filipas123/autonomous-computer/4x-6000/photos/4gpu/introduction/rack3.jpg

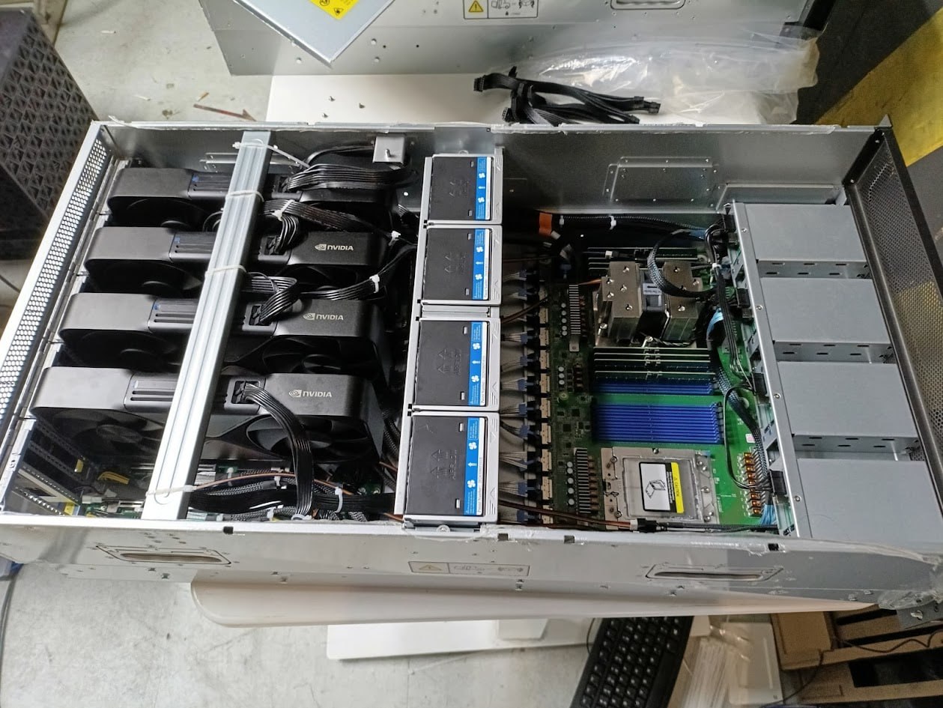
4x-6000/photos/4gpu/introduction/rack3.jpg
