filipas123/autonomous-computer/4x-6000/photos/4gpu/preparing/ee/card1.jpg

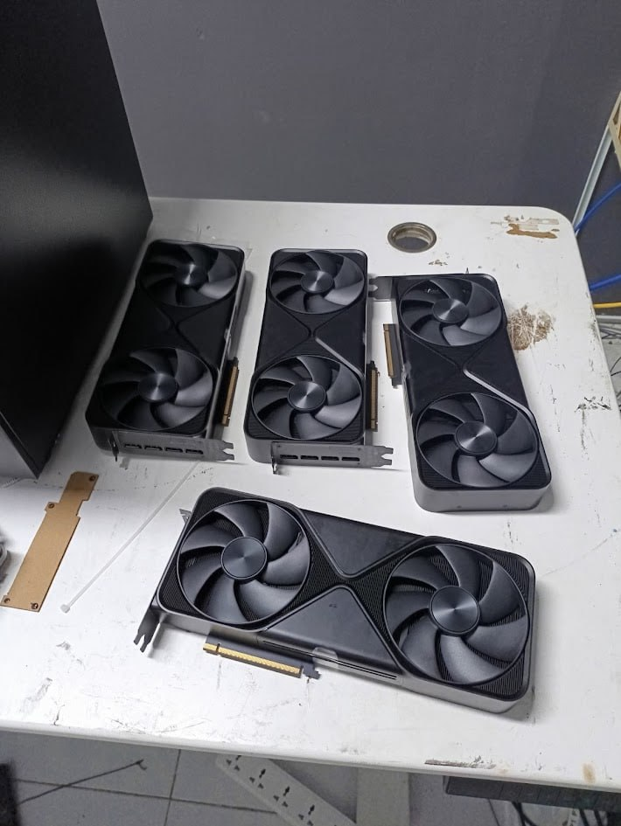
4x-6000/photos/4gpu/preparing/ee/card1.jpg
