filipas123/autonomous-computer/8x-5090/photos/8gpu/introduction/EdgeAI-8GPU-2.png

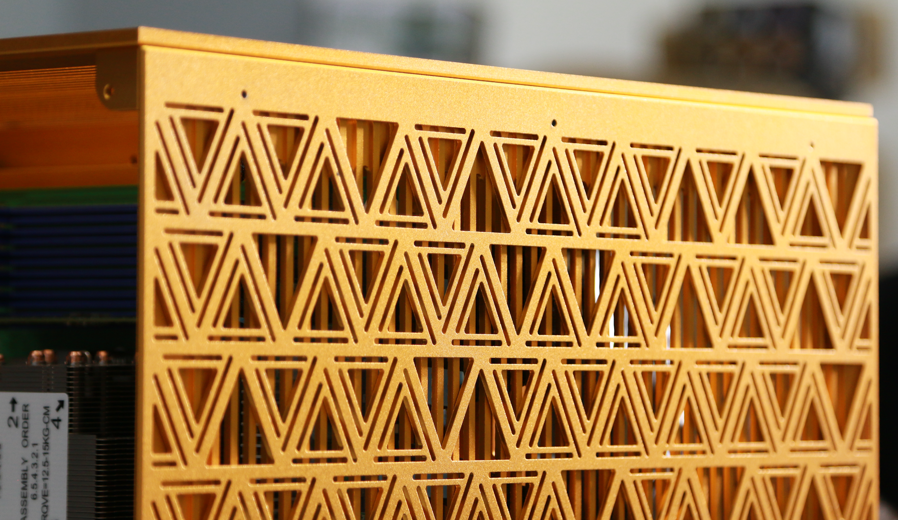
8x-5090/photos/8gpu/introduction/EdgeAI-8GPU-2.png
