filipas123/autonomous-computer/8x-5090/photos/8gpu/preparing/ee/inside-8card.jpg

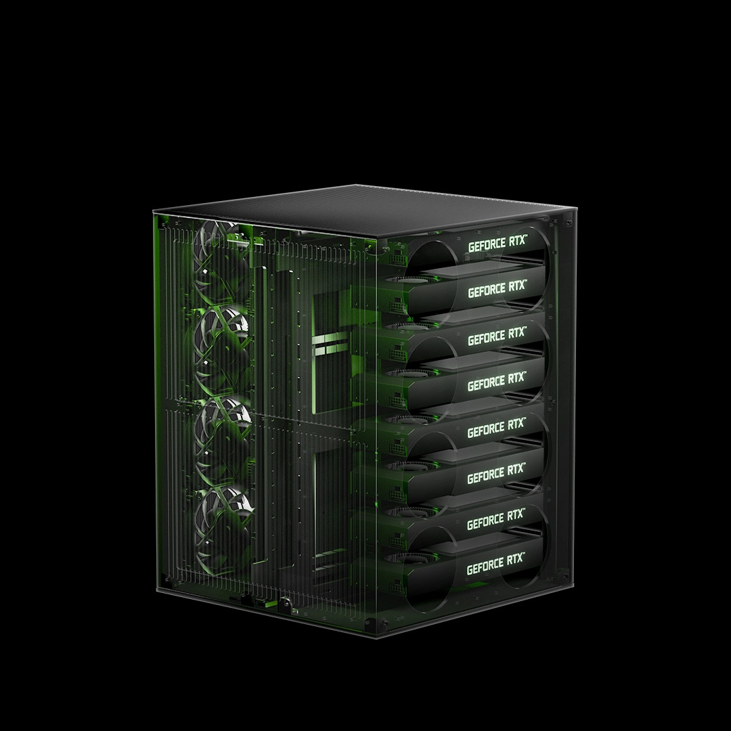
8x-5090/photos/8gpu/preparing/ee/inside-8card.jpg
