filipas123/autonomous-computer/4x-5090/step_models/Part 1 - Bottom.step

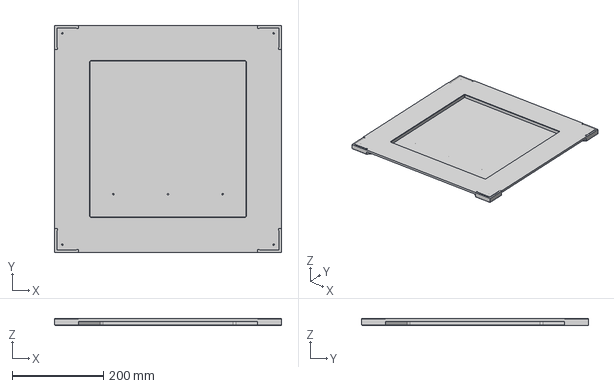
[picture p86: CAD file, 2026-07-07]
4x-5090/step_models/Part 1 - Bottom.step
498.0 x 498.0 x 15.0 mm
