filipas123/autonomous-computer/8x-5090/step_models/GPU mount.step

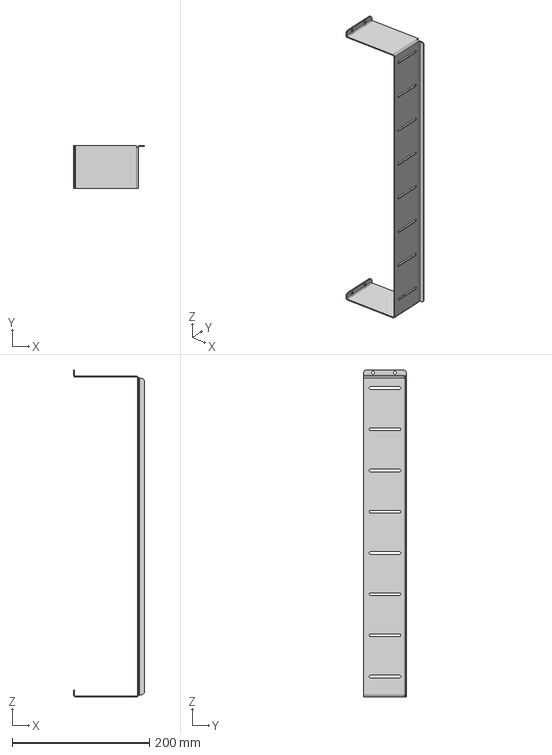
[picture p87: CAD file, 2025-08-18]
8x-5090/step_models/GPU mount.step
103.5 x 63.0 x 476.0 mm
