filipas123/autonomous-computer/2x-5090/step_models/Part 5 - Middle.step

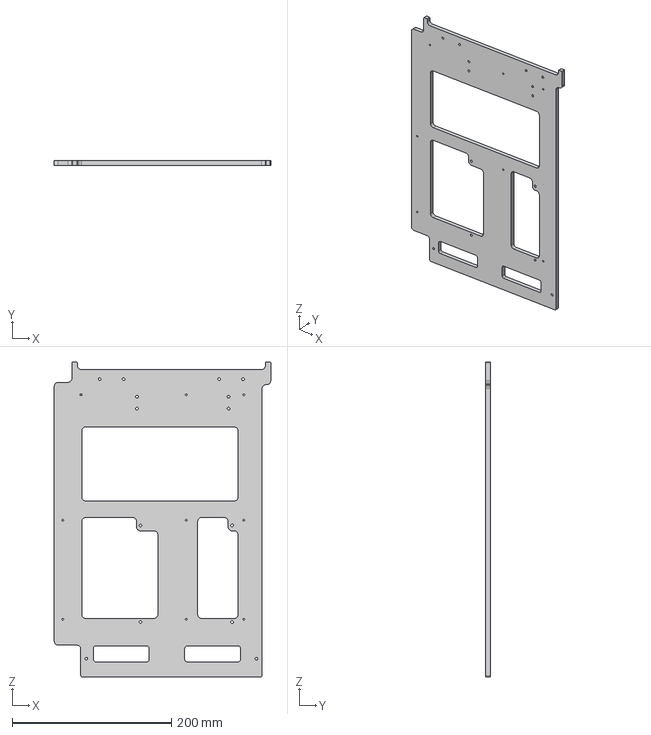
[picture p88: CAD file, 2026-06-01]
2x-5090/step_models/Part 5 - Middle.step
271.9 x 6.00 x 395.5 mm
