filipas123/autonomous-computer/4x-5090/step_models/9 Fan mount.step

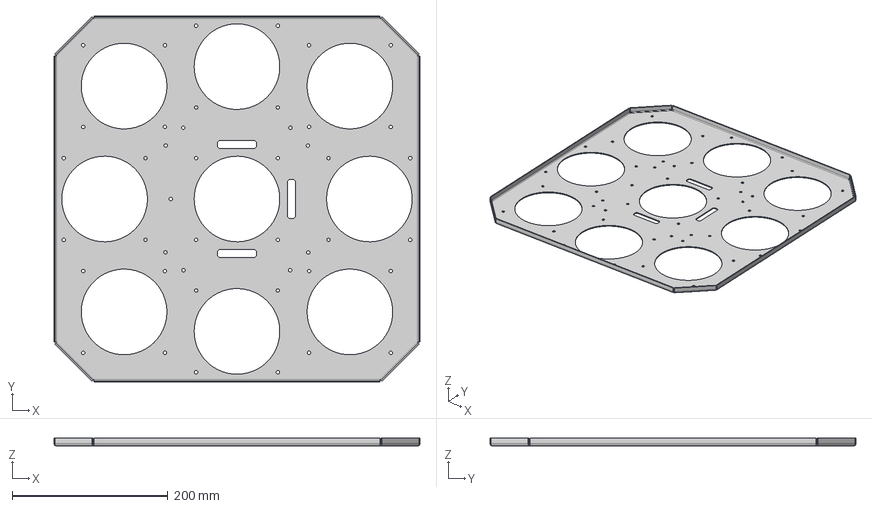
[picture p89: CAD file, 2026-07-07]
4x-5090/step_models/9 Fan mount.step
470.0 x 470.0 x 10.0 mm
