filipas123/autonomous-computer/8x-5090/step_models/Part 5 - Bottom.step

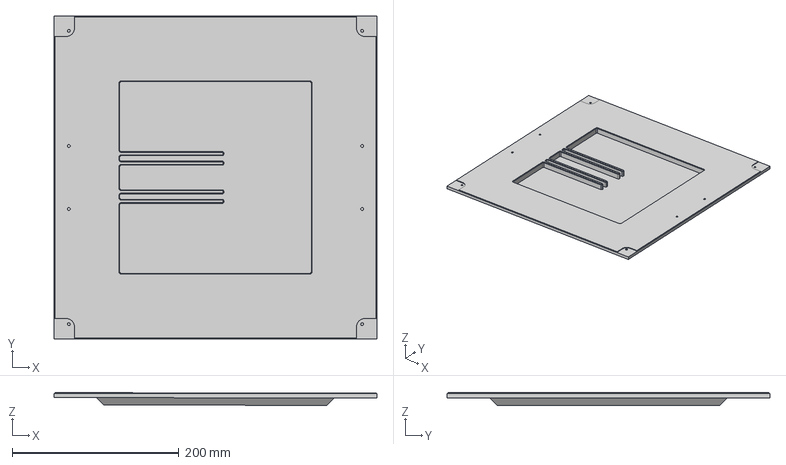
[picture p90: CAD file, 2025-08-18]
8x-5090/step_models/Part 5 - Bottom.step
387.6 x 387.6 x 15.0 mm
