filipas123/autonomous-computer/2x-5090/step_models/Part 4 - Bottom.step

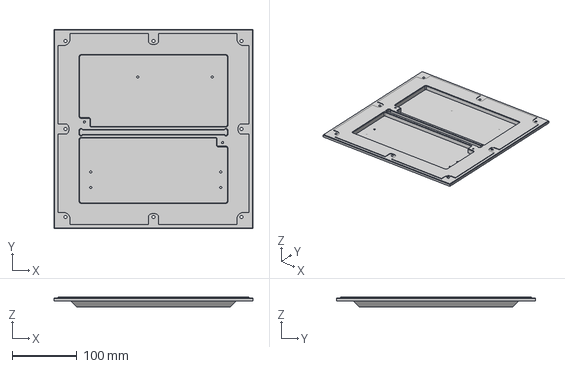
[picture p91: CAD file, 2026-06-01]
2x-5090/step_models/Part 4 - Bottom.step
307.6 x 307.6 x 15.0 mm
