filipas123/autonomous-computer/4x-5090/step_models/GPU mount.step

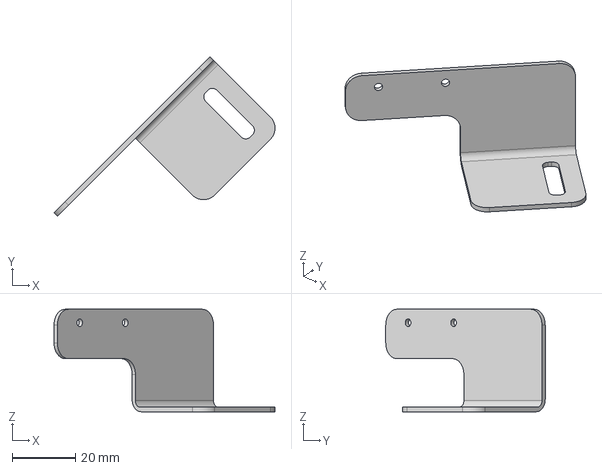
[picture p92: CAD file, 2026-07-07]
4x-5090/step_models/GPU mount.step
70.0 x 50.6 x 32.5 mm
