filipas123/autonomous-computer/8x-5090/step_models/Support.step

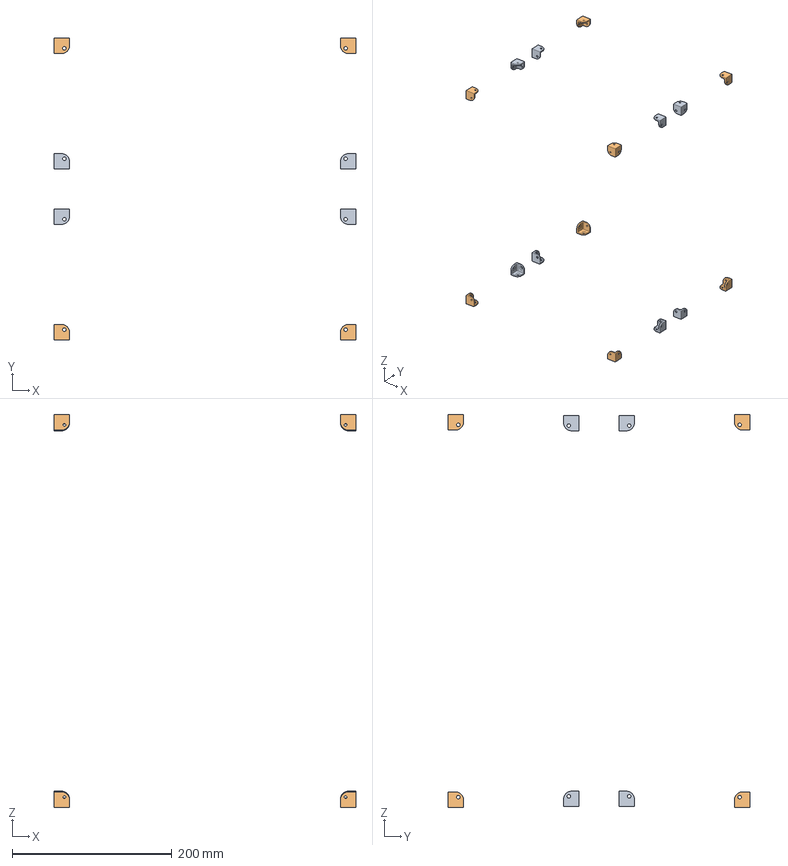
[picture p93: CAD file, 2025-08-18]
8x-5090/step_models/Support.step
378.0 x 378.0 x 492.0 mm
Bat goc x 8
Bat goc (1) x 4
Bat goc (1)(Mirror)
Bat goc (1) (2)(Mirror)
Bat goc (1) (3)(Mirror)
Bat goc (1) (1)(Mirror)
