filipas123/autonomous-computer/2x-5090/step_models/GPU mount 1.step

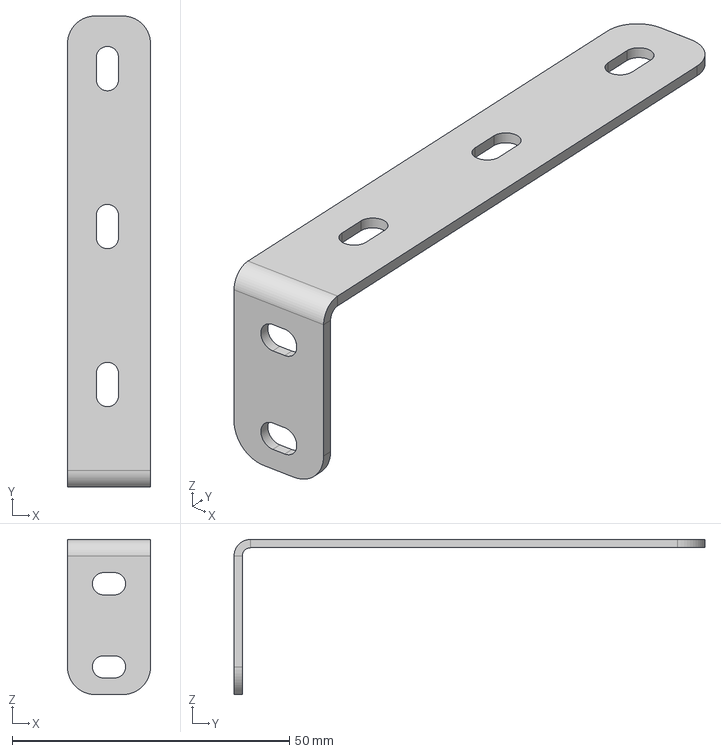
[picture p94: CAD file, 2026-06-01]
2x-5090/step_models/GPU mount 1.step
15.0 x 85.0 x 28.0 mm
