filipas123/autonomous-computer/4x-5090/step_models/Part 3 - Top.step

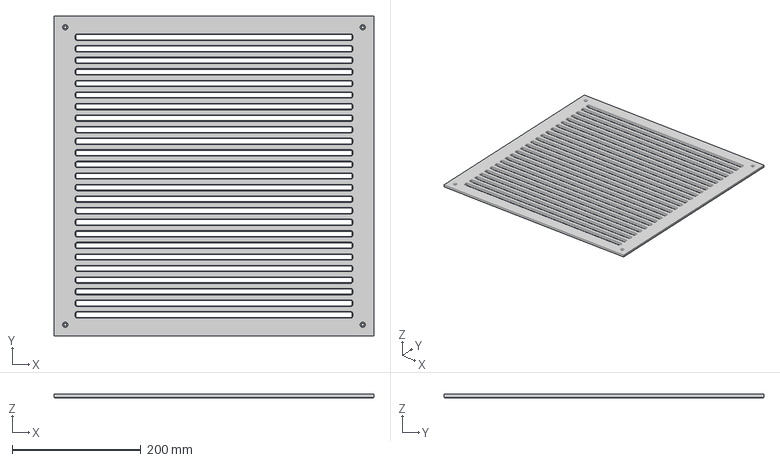
[picture p95: CAD file, 2026-07-07]
4x-5090/step_models/Part 3 - Top.step
498.0 x 498.0 x 6.00 mm
