filipas123/autonomous-computer/8x-5090/step_models/Part 1 - GPU plate.step

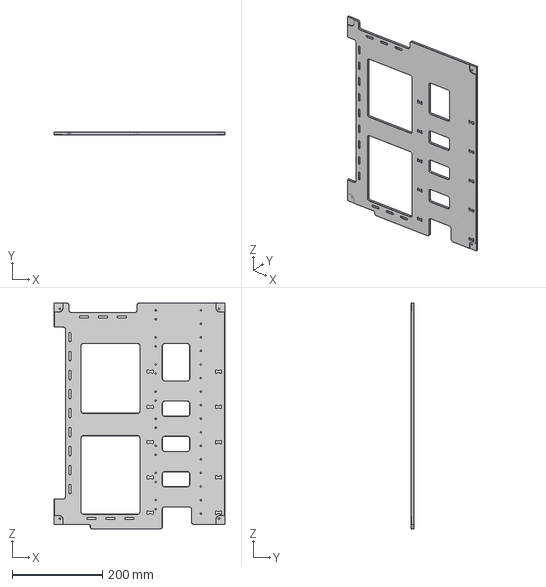
[picture p96: CAD file, 2025-08-18]
8x-5090/step_models/Part 1 - GPU plate.step
378.0 x 6.00 x 500.0 mm
