filipas123/autonomous-computer/4x-5090/step_models/Part 6 - Corner 2.step

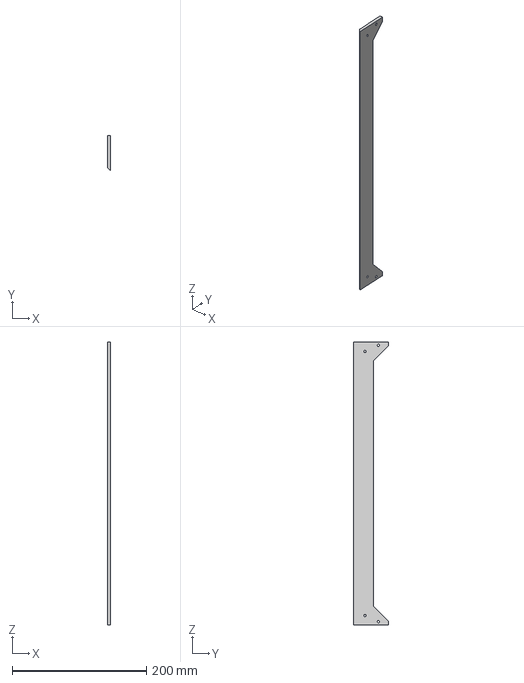
[picture p97: CAD file, 2026-07-07]
4x-5090/step_models/Part 6 - Corner 2.step
5.00 x 52.0 x 421.5 mm
