filipas123/autonomous-computer/8x-5090/step_models/Ethernet mount.step

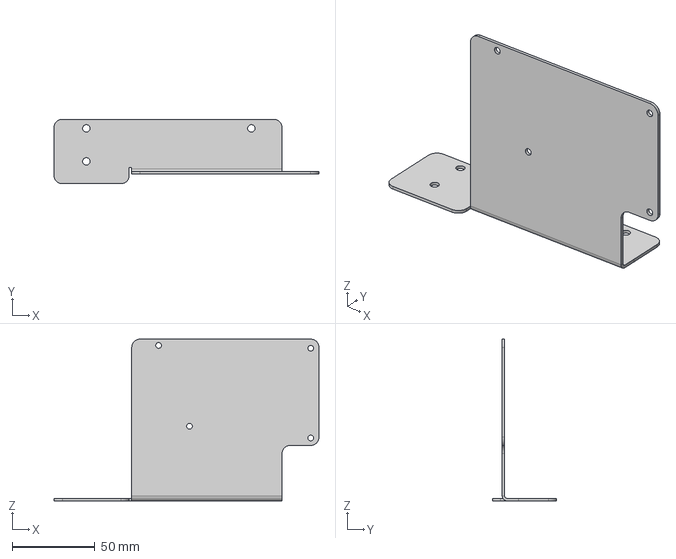
[picture p98: CAD file, 2025-08-18]
8x-5090/step_models/Ethernet mount.step
160.6 x 39.0 x 98.0 mm
