filipas123/autonomous-computer/4x-5090/step_models/Part 2 - Back.step

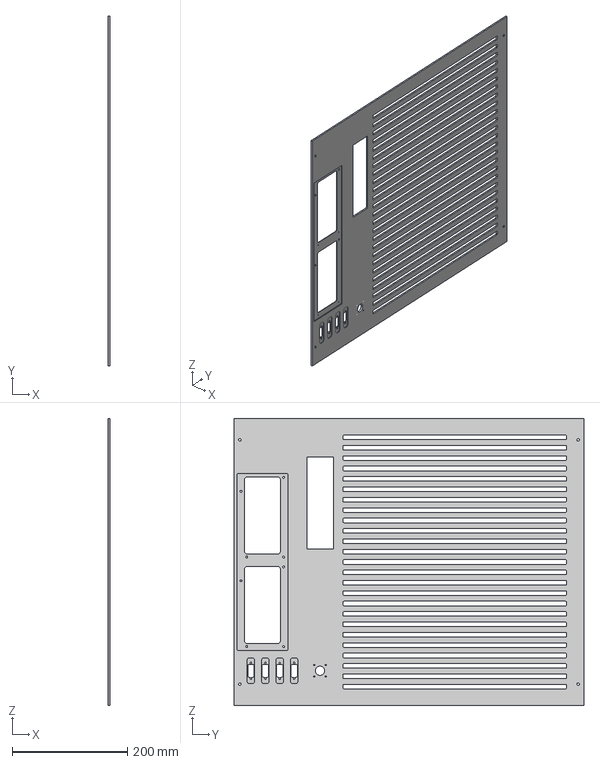
[picture p99: CAD file, 2026-07-07]
4x-5090/step_models/Part 2 - Back.step
4.00 x 606.5 x 498.0 mm
