filipas123/autonomous-computer/4x-5090/step_models/Corner mount.step

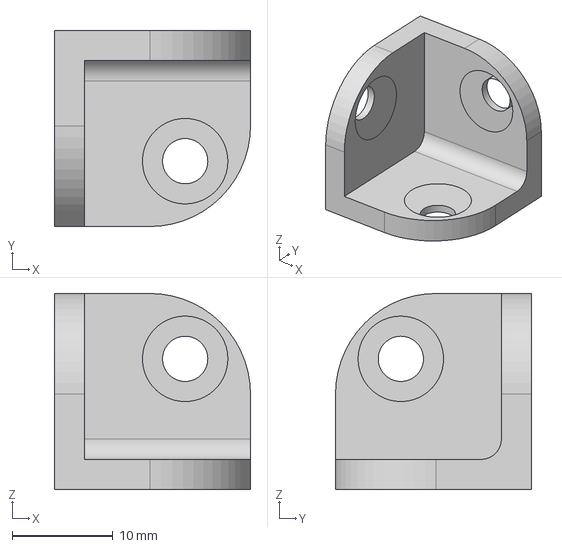
[picture p101: CAD file, 2026-07-07]
4x-5090/step_models/Corner mount.step
19.5 x 19.5 x 19.5 mm
