filipas123/autonomous-computer/4x-5090/step_models/Part 5 - Corner 1.step

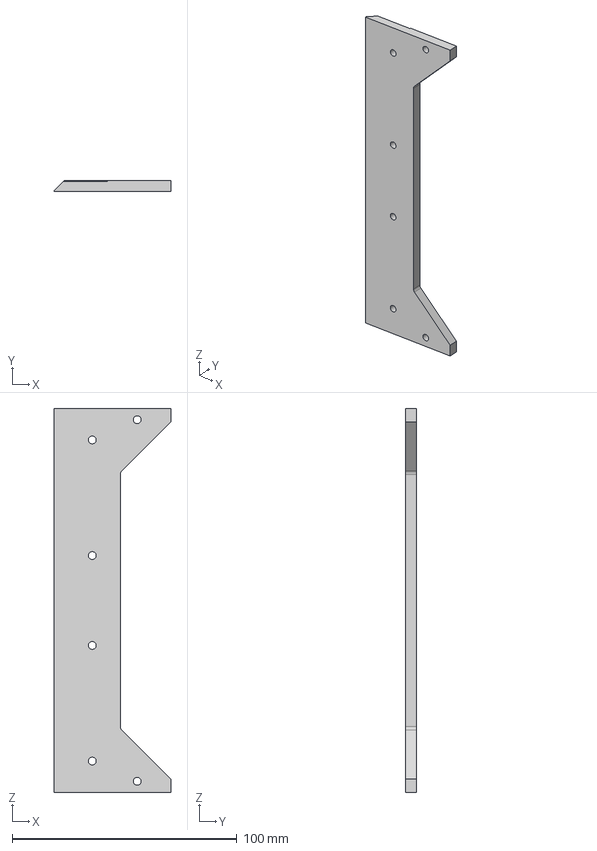
[picture p102: CAD file, 2026-07-07]
4x-5090/step_models/Part 5 - Corner 1.step
52.0 x 5.00 x 171.0 mm
