filipas123/autonomous-computer/4x-5090/step_models/Part 4 - Middle.step

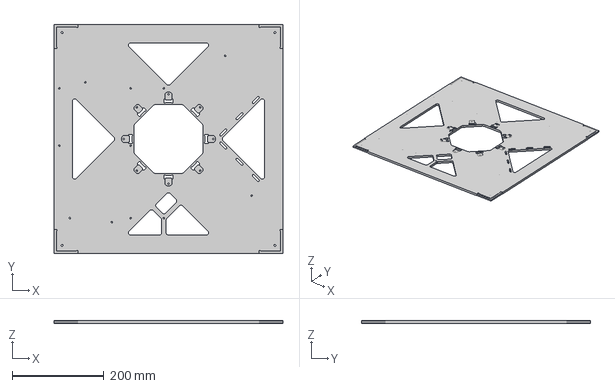
[picture p103: CAD file, 2026-07-07]
4x-5090/step_models/Part 4 - Middle.step
498.0 x 498.0 x 6.00 mm
