filipas123/autonomous-computer/4x-5090/step_models/Part 7 - GPU Holder 1.step

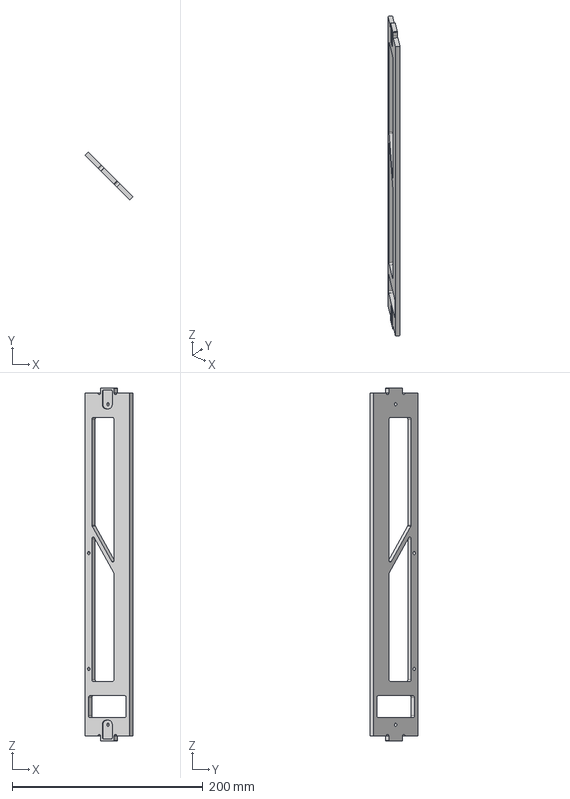
[picture p104: CAD file, 2026-07-07]
4x-5090/step_models/Part 7 - GPU Holder 1.step
50.2 x 50.2 x 370.0 mm
