filipas123/autonomous-computer/4x-5090/step_models/L mount.step

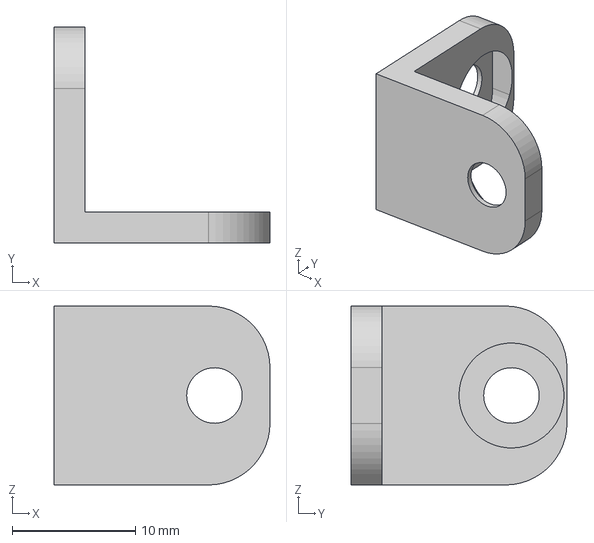
[picture p105: CAD file, 2026-07-07]
4x-5090/step_models/L mount.step
17.5 x 17.5 x 14.5 mm
