filipas123/autonomous-computer/4x-6000/build-4x.jpg

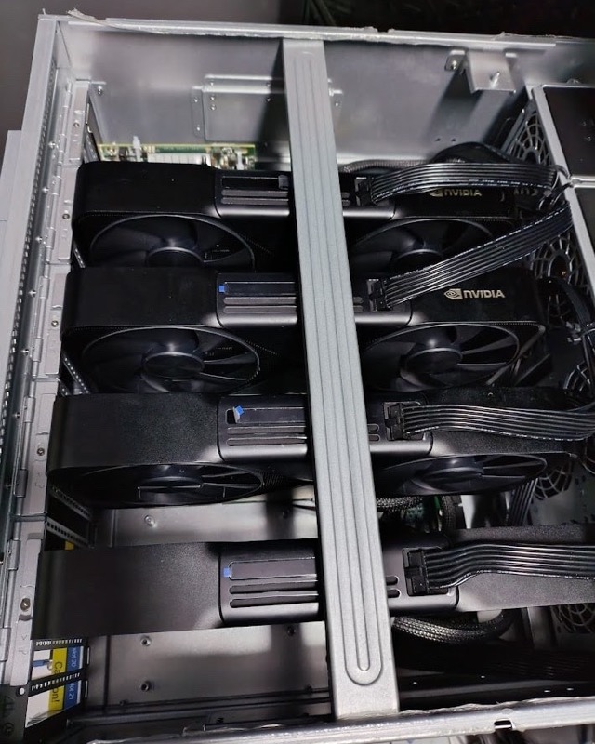
4x-6000/build-4x.jpg
