filipas123/autonomous-computer/8x-5090/build-8x.jpg

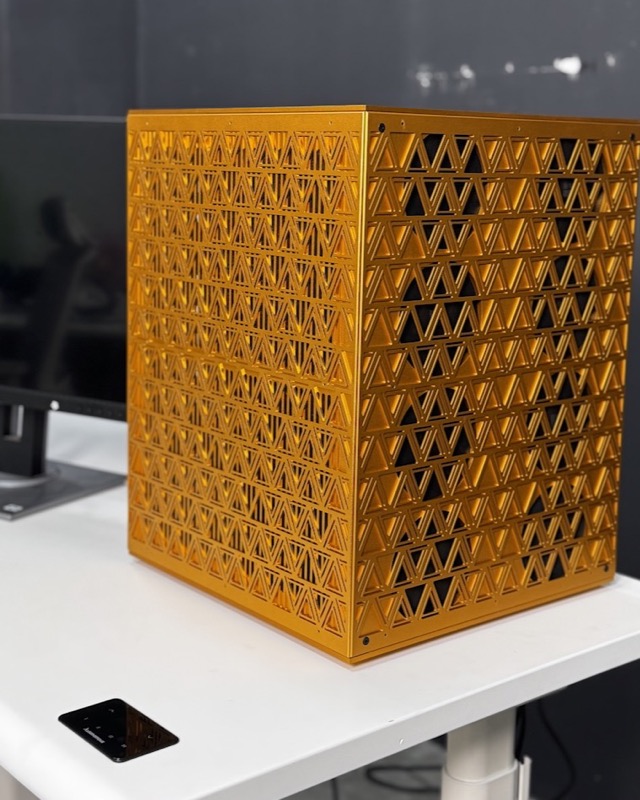
8x-5090/build-8x.jpg
